bryanshellpuppy/Meshtastic3d/RP_Zero2w/PiZero2w_BBQ_Render.jpg

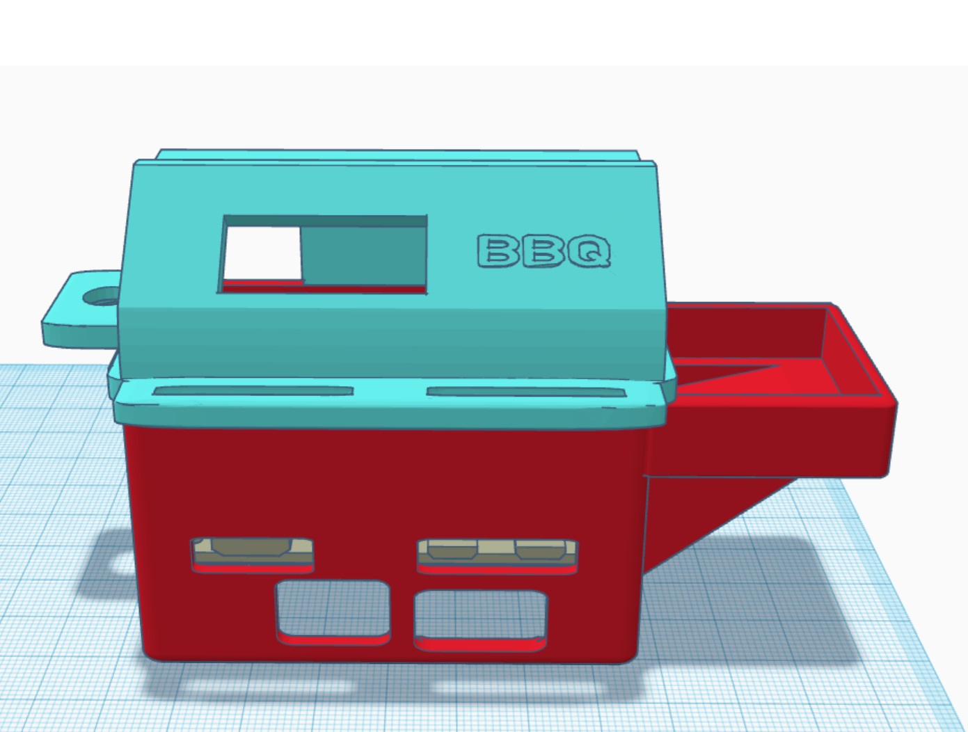
RP_Zero2w/PiZero2w_BBQ_Render.jpg
