bryanshellpuppy/Meshtastic3d/RAK_19007/RAK19007-mini_v8_button-reset-tall.stl

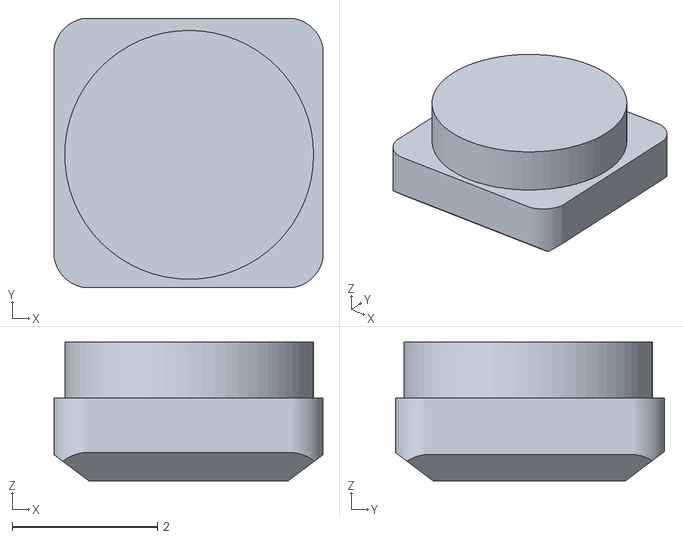
[picture p25: CAD file, 2024-09-05]
RAK_19007/RAK19007-mini_v8_button-reset-tall.stl
3.70 x 3.70 x 1.91
