bryanshellpuppy/Meshtastic3d/RAK_19007/RAK19007-5005_v15_button-plate.stl

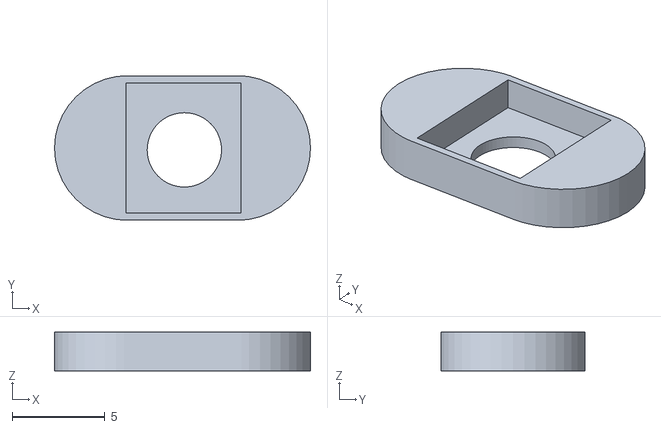
[picture p26: CAD file, 2024-09-05]
RAK_19007/RAK19007-5005_v15_button-plate.stl
13.8 x 7.77 x 2.10
